francofusco/wp3/imgs/cad_export.gif

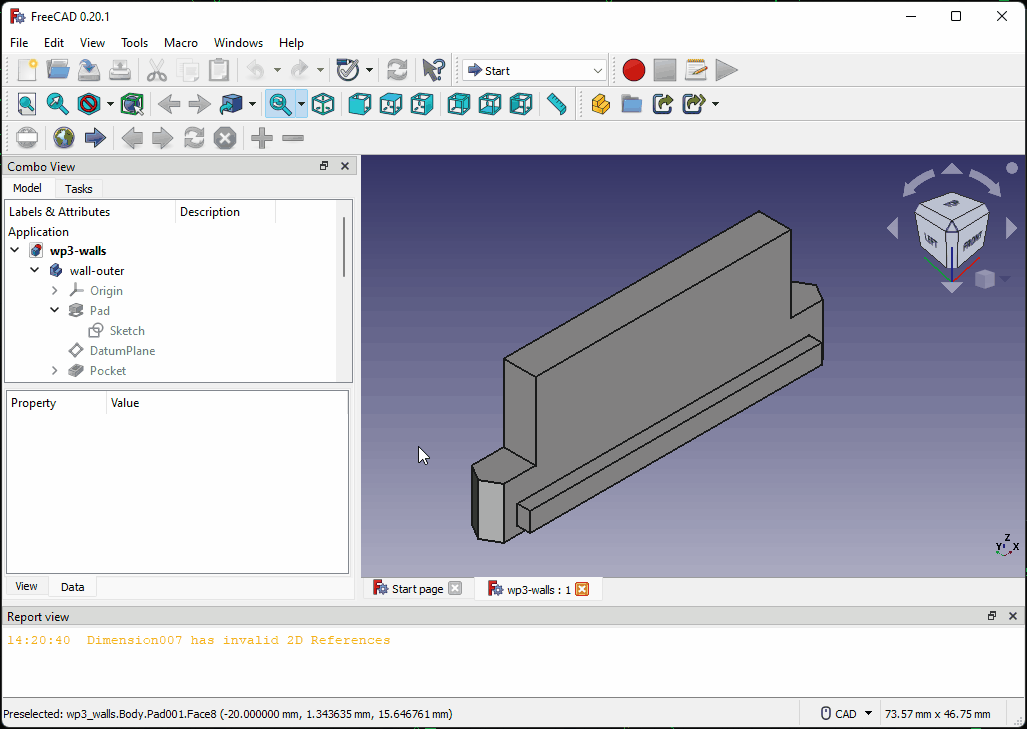
imgs/cad_export.gif
